stairs1/stim-music/hardware/SPICE/v2.asc

Q1: pnp; BC857A
Q7: npn; BC847A
R1: res; 470
R2: res; 470
R3: res; 200
R4: res; 200
R_Load: res; 4k
V1: voltage; 9.6
V2: voltage; 12
V3: voltage; 12
V4: voltage; 10.85
Named nets: 0
;op
.dc V4 0 12 0.1
