stairs1/stim-music/hardware/SPICE/current_limiters.asc

Q1: npn; BC847A
Q2: npn; BC847A
Q3: npn; BC847A
Q4: npn; BC847A
Q5: npn; BC847A
Q6: npn; BC847A
Q7: npn
Q8: pnp; BC857B
Q9: pnp; BC857B
Q10: pnp; BC857B
Q11: pnp; BC857B
R1: res; 500
R2: res; 500
R_Bias1: res; 210k
R_Bias2: res; 1170
R_Bias3: res; 210k
R_Load: res; 2k
R_Sense1: res; 70
R_Sense2: res; 210k
R_Sense3: res; 100
V1: voltage; 8.2
V2: voltage; 12
V3: voltage; 12
V4: voltage; 12
Named nets: 0
.dc V3 0 12 0.1
